Oak-Development-Technologies/IcyBlue/Images/IcyBlue-Bottom-2.jpg

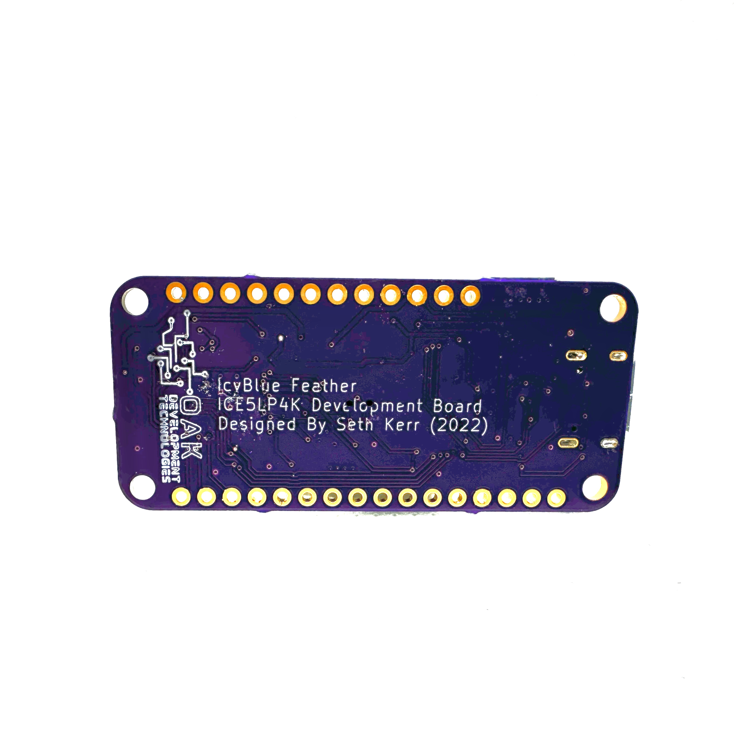
Images/IcyBlue-Bottom-2.jpg
