Oak-Development-Technologies/IcyBlue/Images/IcyBlue-OffSet-2.jpg

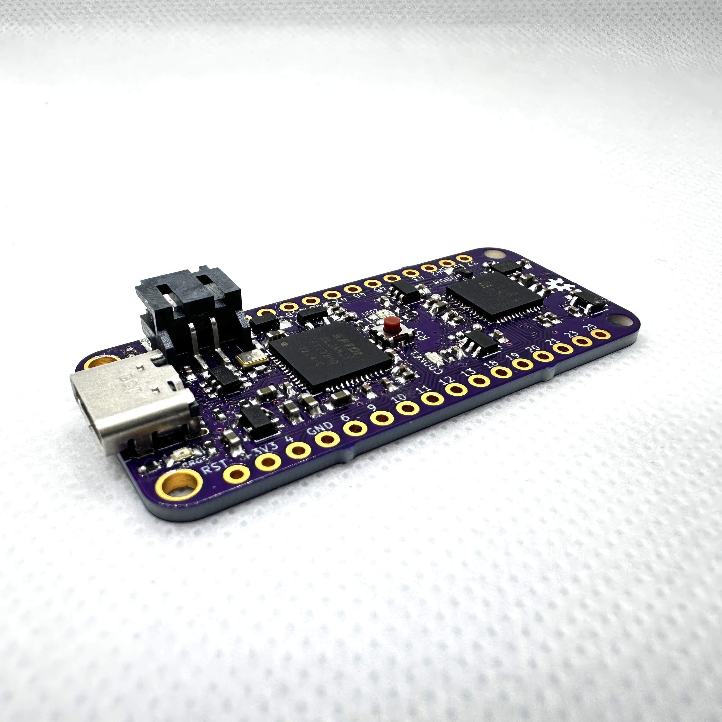
Images/IcyBlue-OffSet-2.jpg
