Oak-Development-Technologies/IcyBlue/Images/IMG_2197.jpg

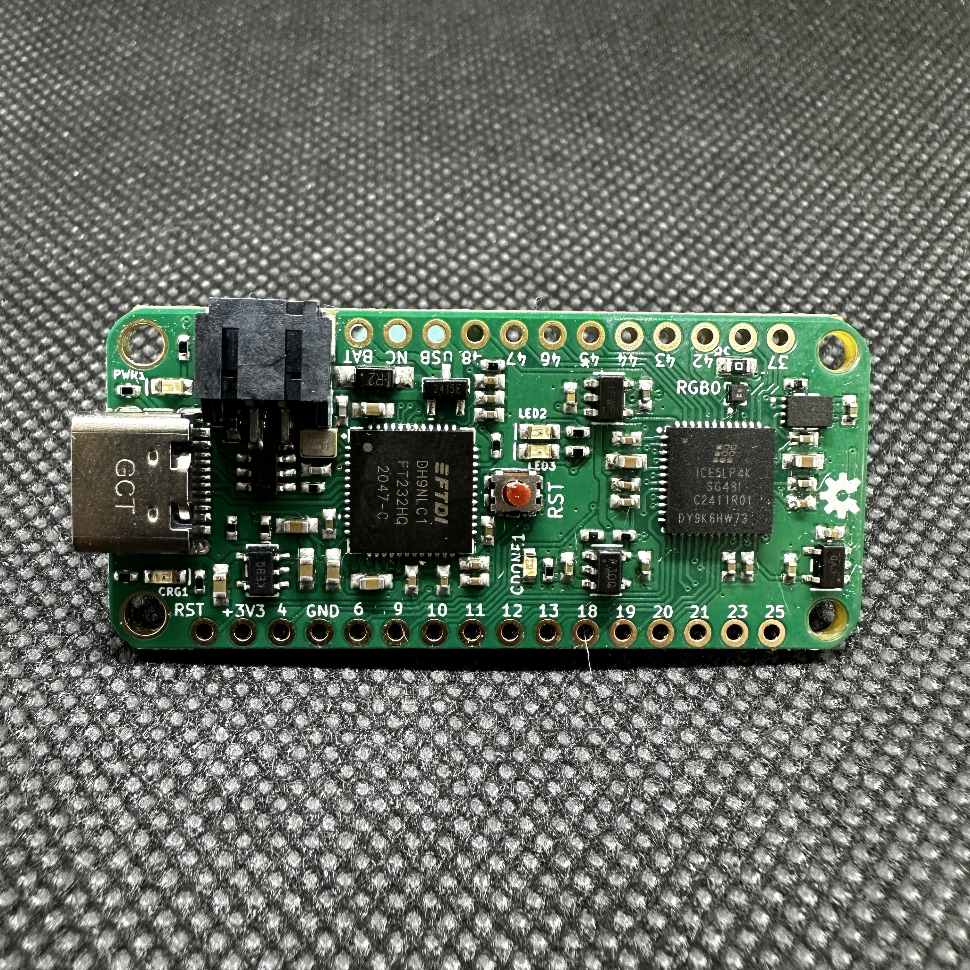
Images/IMG_2197.jpg
