Oak-Development-Technologies/IcyBlue/Images/IMG_2198.jpg

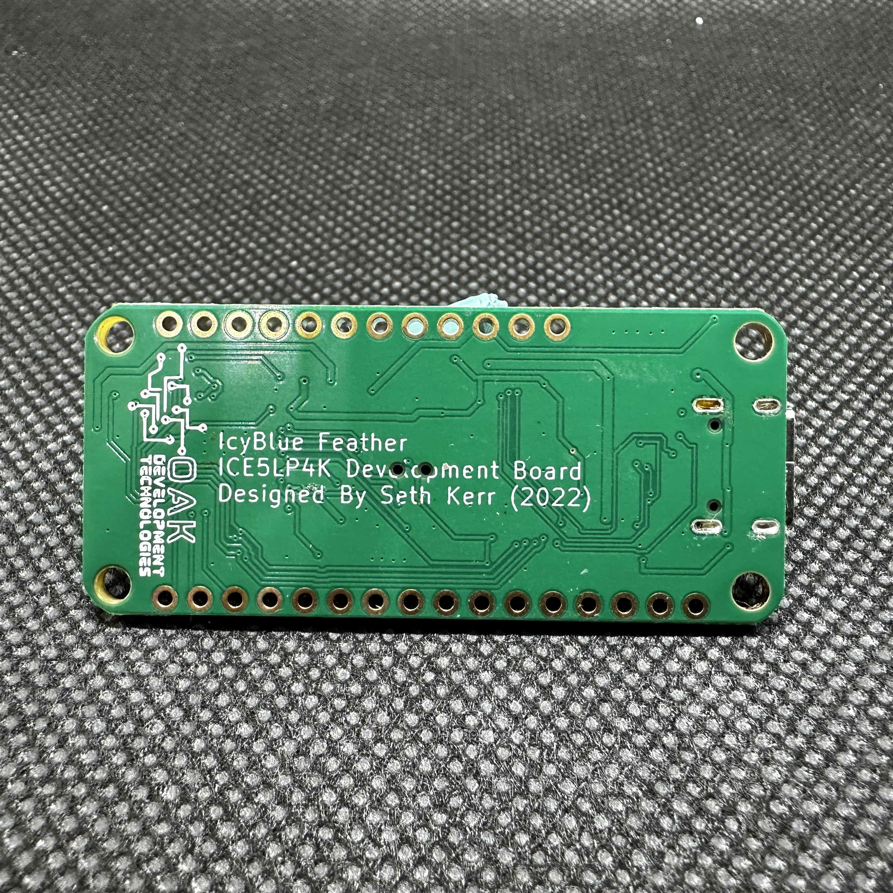
Images/IMG_2198.jpg
